cwgstreet/cloudSmoker/Enclosure/models/EC11 rotary encoder/ec11-rotary-encoder2.png

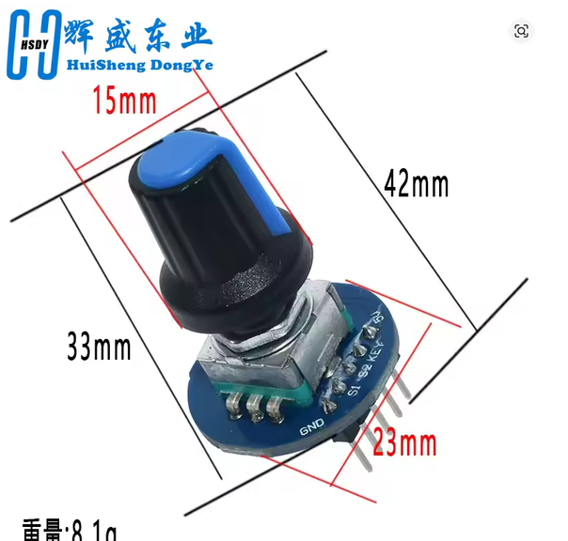
Enclosure/models/EC11 rotary encoder/ec11-rotary-encoder2.png
