cwgstreet/cloudSmoker/Enclosure/models/EC11 rotary encoder/ec11-rotary-encoder.png

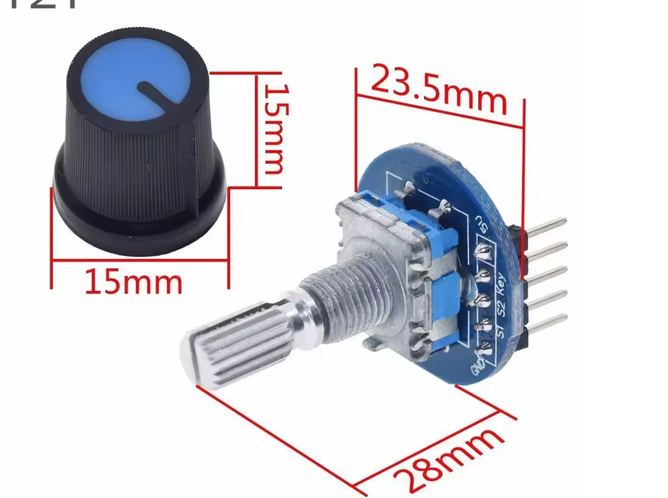
Enclosure/models/EC11 rotary encoder/ec11-rotary-encoder.png
