cwgstreet/cloudSmoker/Enclosure/models/GC9A01_display/GC9A01_display-dimensions.jpg

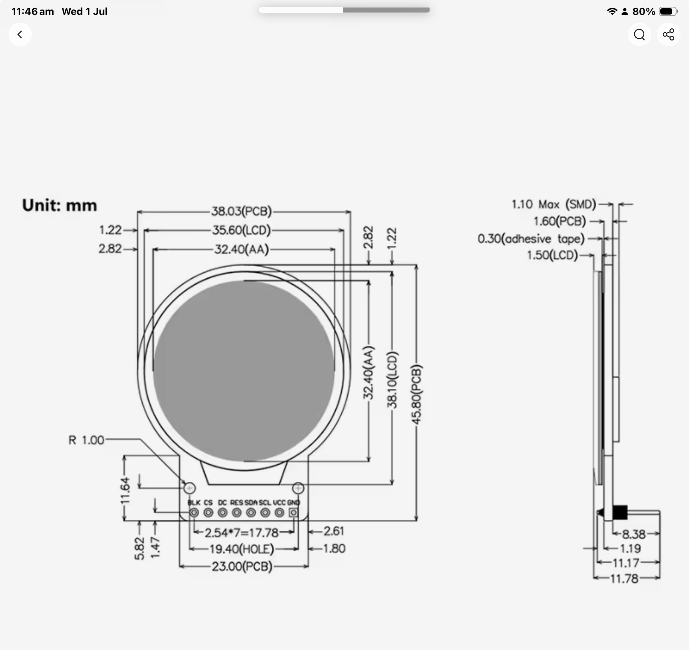
Enclosure/models/GC9A01_display/GC9A01_display-dimensions.jpg
