cwgstreet/cloudSmoker/Hardware/KiCad9/svg_files/ADS-thermistor_closeup.png

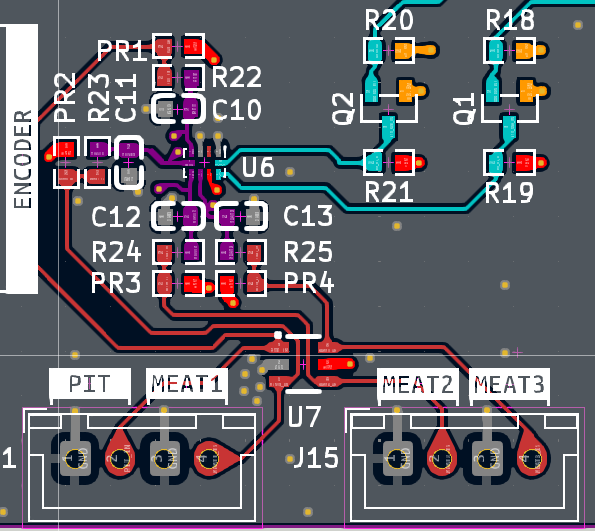
Hardware/KiCad9/svg_files/ADS-thermistor_closeup.png
