cwgstreet/cloudSmoker/Hardware/KiCad9/svg_files/pcb_dashboard2.png

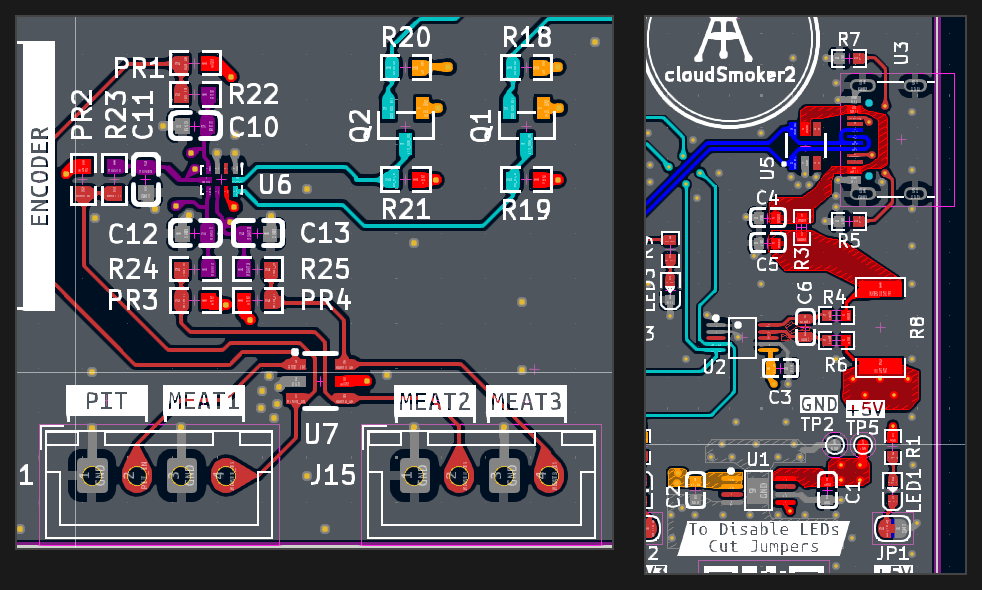
Hardware/KiCad9/svg_files/pcb_dashboard2.png
