cwgstreet/cloudSmoker/Hardware/KiCad9/svg_files/view1_all.png

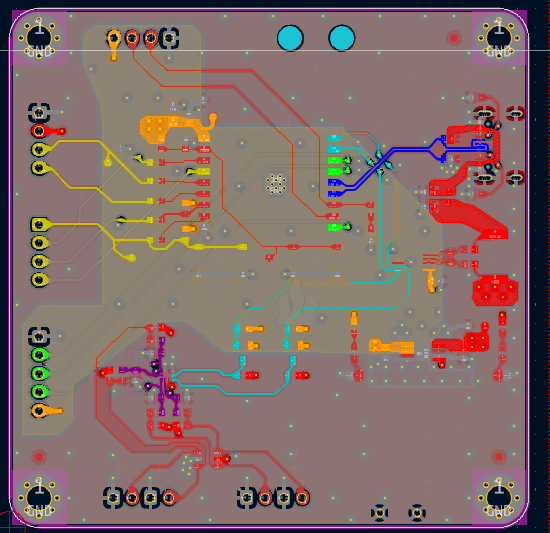
Hardware/KiCad9/svg_files/view1_all.png
