cwgstreet/cloudSmoker/Hardware/KiCad9/svg_files/view2_top.png

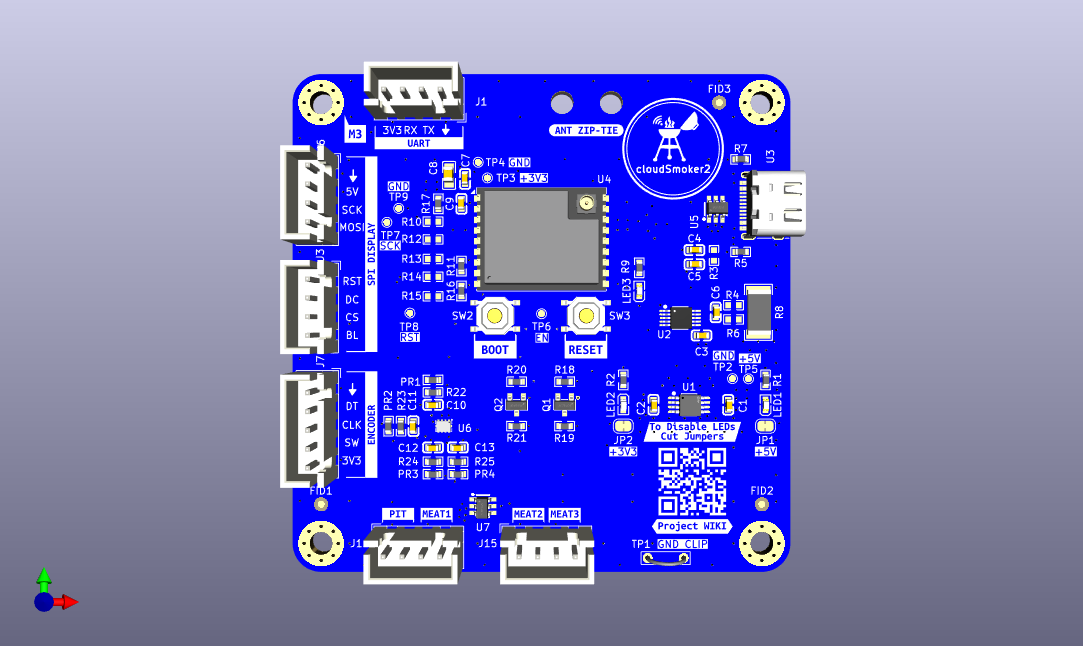
Hardware/KiCad9/svg_files/view2_top.png
