cwgstreet/cloudSmoker/Images/2-CH Logic Level Converter.jpg

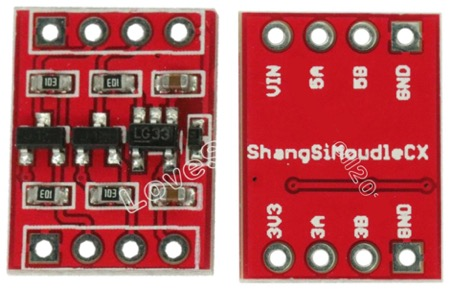
Images/2-CH Logic Level Converter.jpg
