cwgstreet/cloudSmoker/Images/Breadboard2.jpg

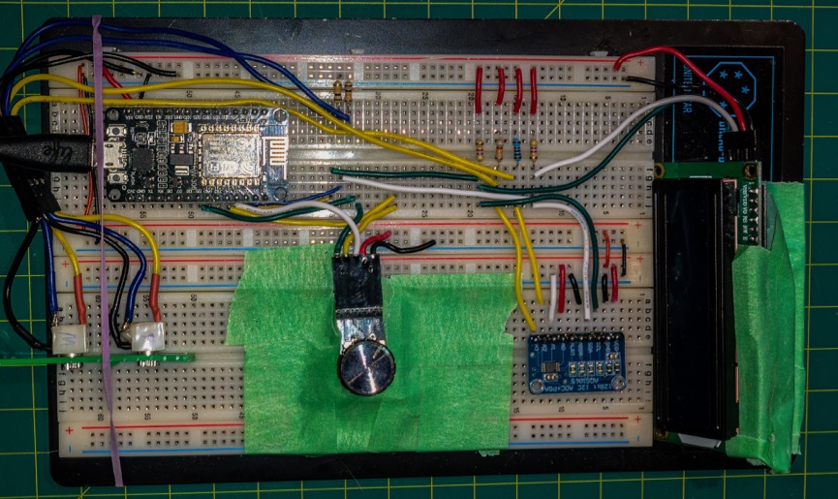
Images/Breadboard2.jpg
