cwgstreet/cloudSmoker/Images/Breadboard.jpg

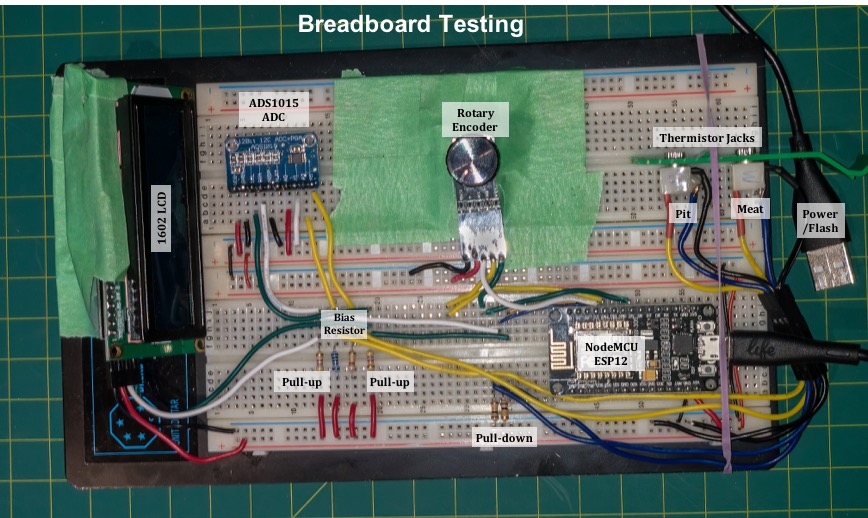
Images/Breadboard.jpg
