cwgstreet/cloudSmoker/Images/CD4066 equivalent pin out.jpg

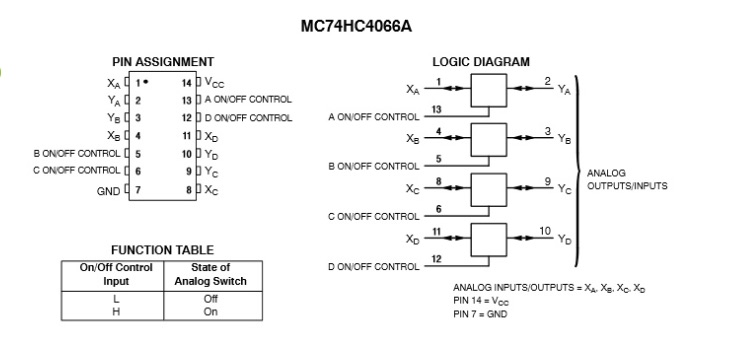
Images/CD4066 equivalent pin out.jpg
