cwgstreet/cloudSmoker/Images/CloudSmoker2 graphic.png

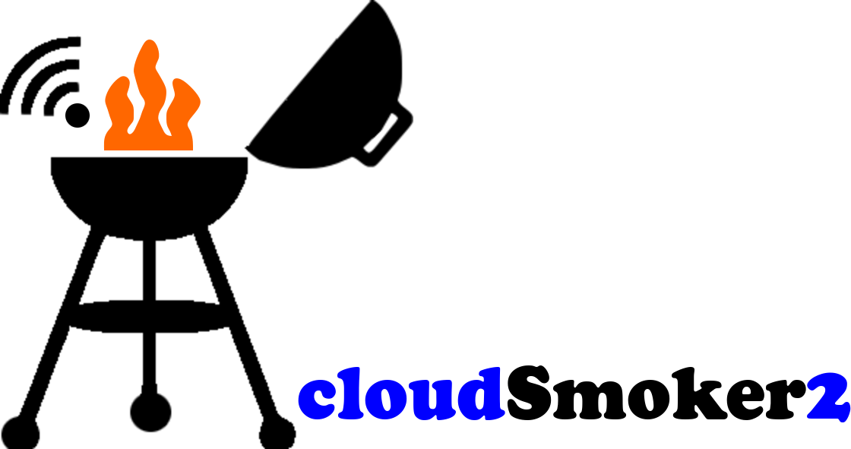
Images/CloudSmoker2 graphic.png
