cwgstreet/cloudSmoker/Images/cloudSmoker2_breadboard_powered.jpg

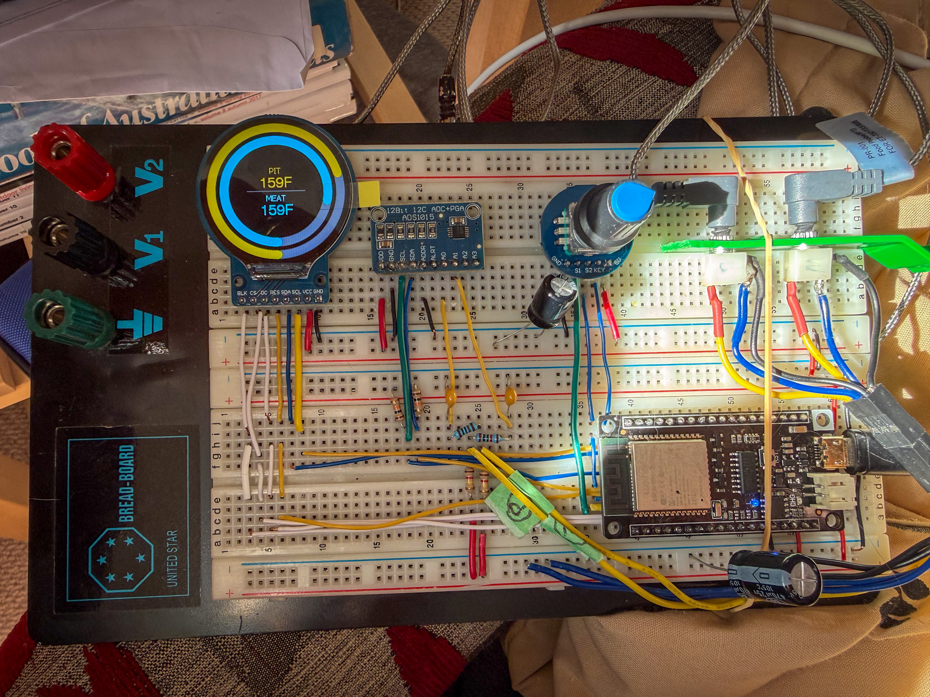
Images/cloudSmoker2_breadboard_powered.jpg
