cwgstreet/cloudSmoker/Images/cloudSmoker2_breadboard_with_ESP32 annotated.jpg

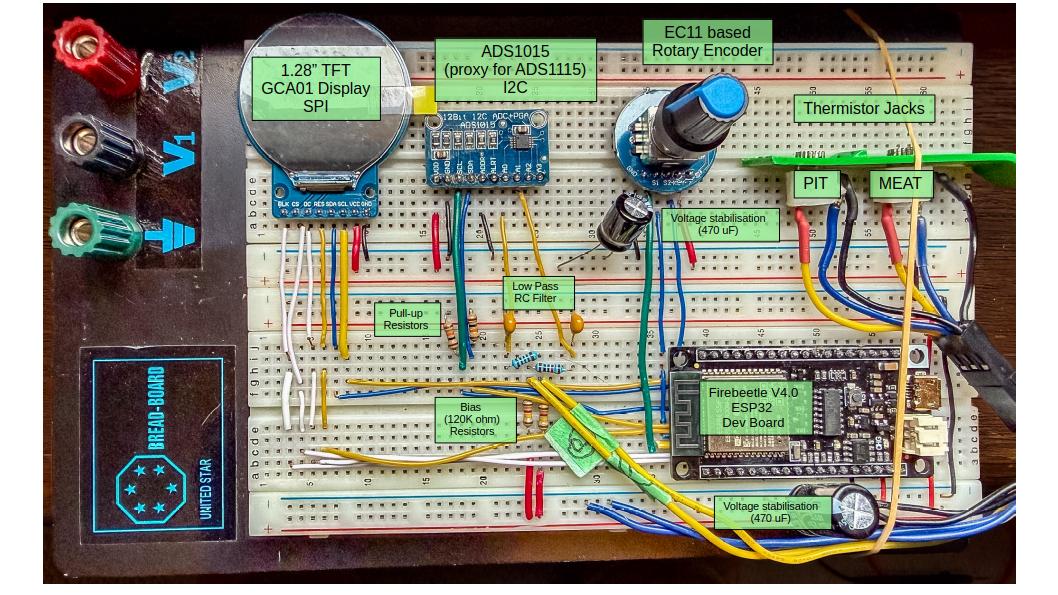
Images/cloudSmoker2_breadboard_with_ESP32 annotated.jpg
