cwgstreet/cloudSmoker/Images/cloudSmoker2_breadboard_with_ESP32.jpg

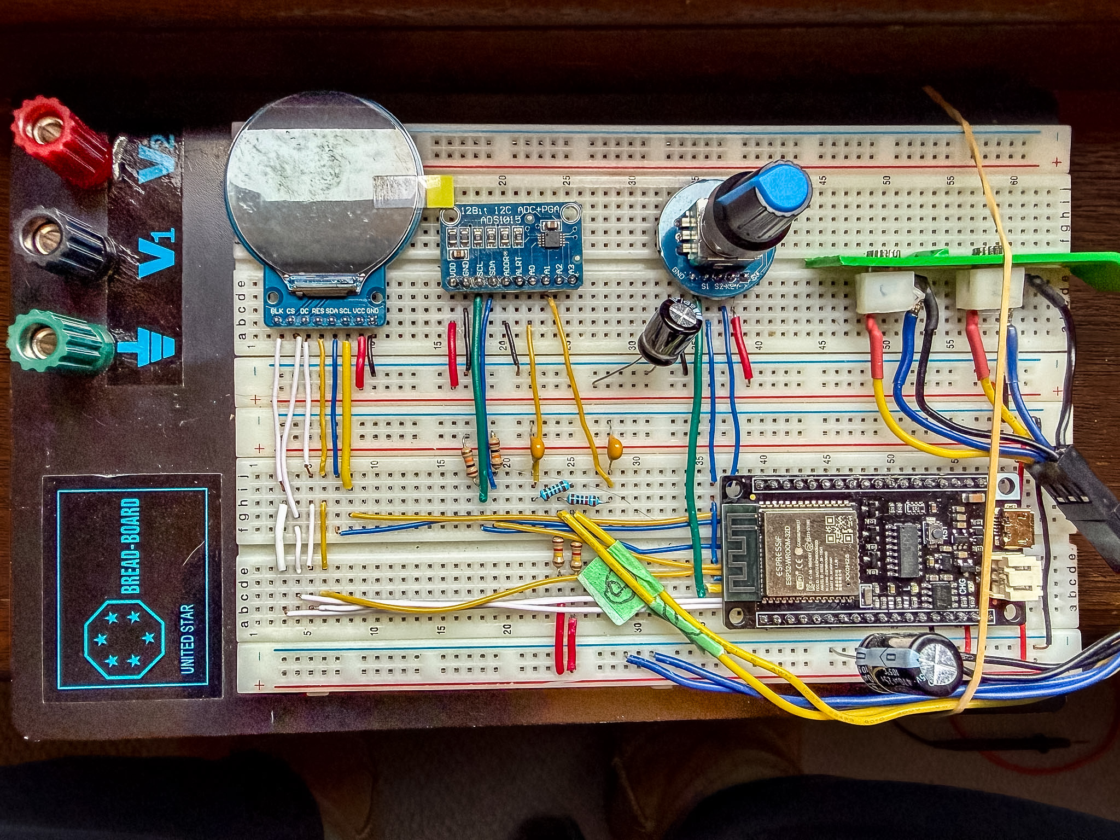
Images/cloudSmoker2_breadboard_with_ESP32.jpg
