cwgstreet/cloudSmoker/Images/cloudSmoker2_breadboard_without_ESP32.jpg

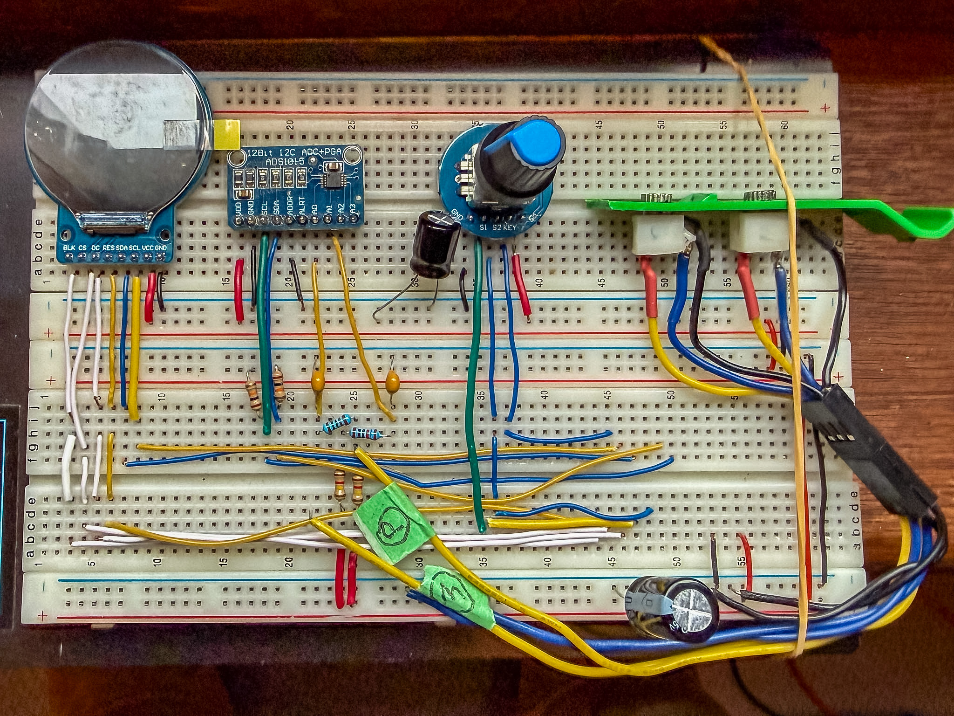
Images/cloudSmoker2_breadboard_without_ESP32.jpg
