cwgstreet/cloudSmoker/Images/cloudSmoker2_display_powered.jpg

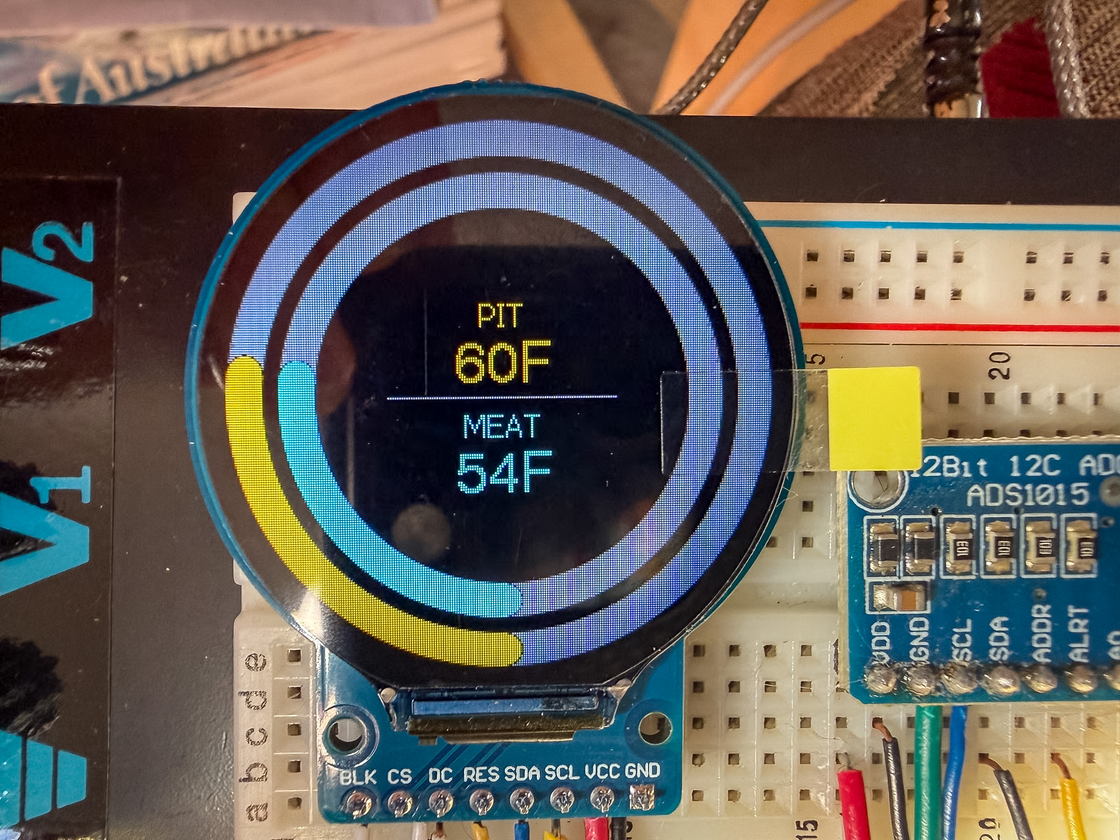
Images/cloudSmoker2_display_powered.jpg
