cwgstreet/cloudSmoker/Images/cloudSmoker brisket dashboard.png

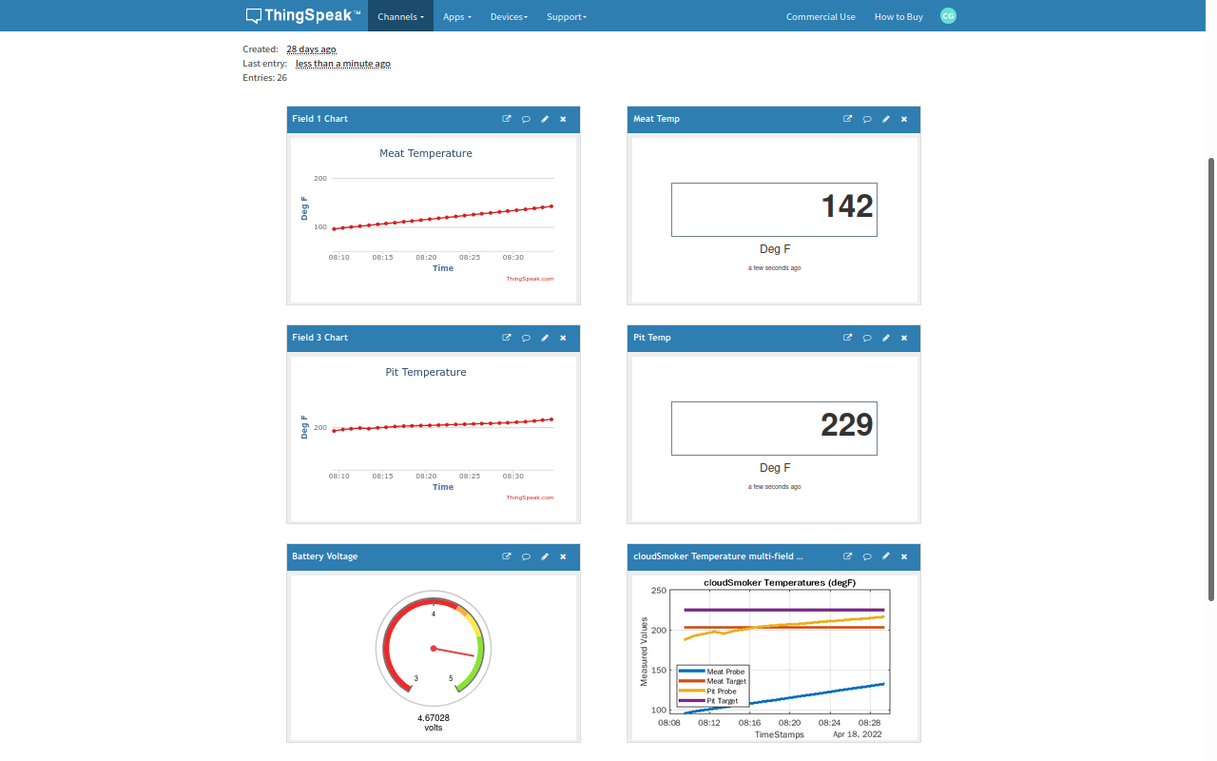
Images/cloudSmoker brisket dashboard.png
