cwgstreet/cloudSmoker/Images/CloudSmoker state diagram2.jpg

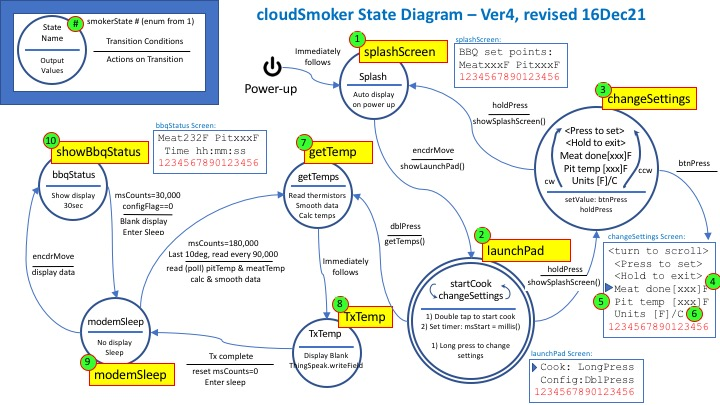
Images/CloudSmoker state diagram2.jpg
