cwgstreet/cloudSmoker/Images/CloudSmoker-breadboard.jpg

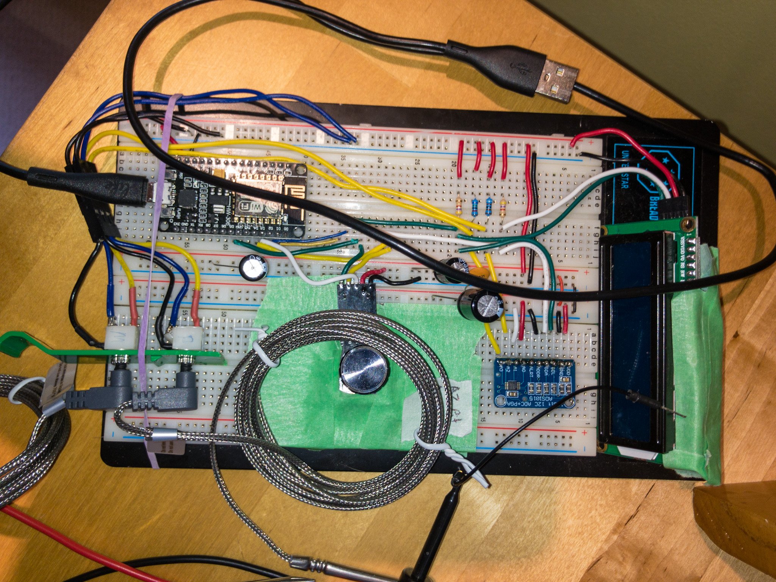
Images/CloudSmoker-breadboard.jpg
