cwgstreet/cloudSmoker/Images/cloudSmoker-fritzing.jpg

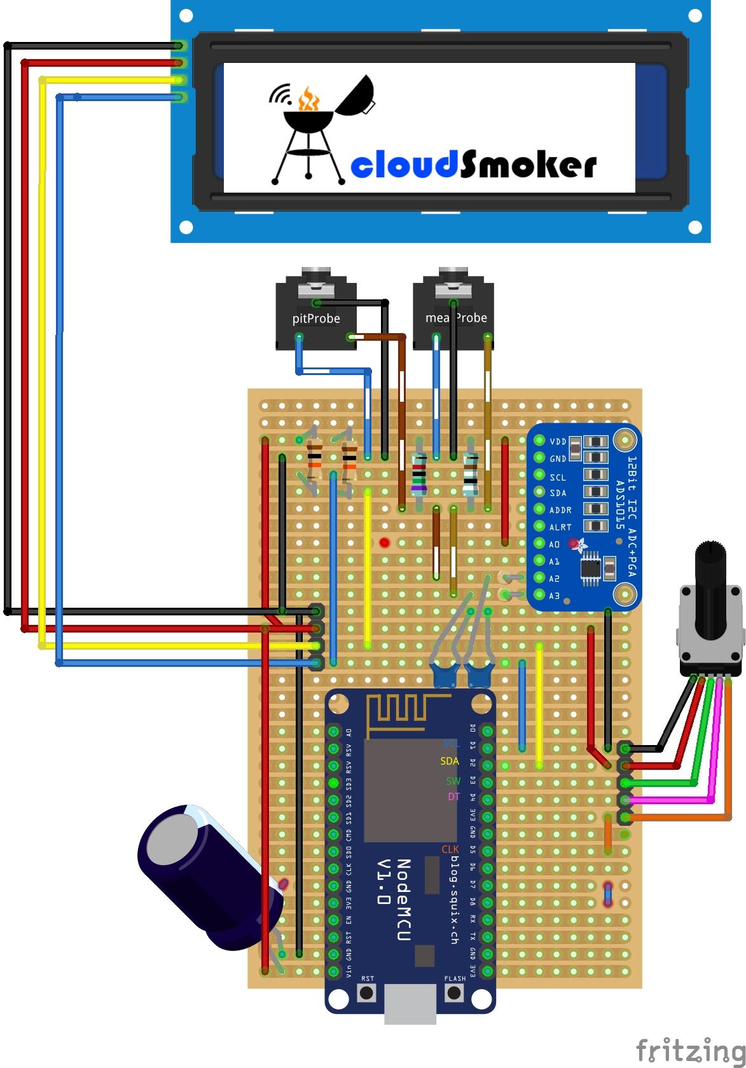
Images/cloudSmoker-fritzing.jpg
