cwgstreet/cloudSmoker/Images/CloudSmoker_breadboard_labelled.jpg

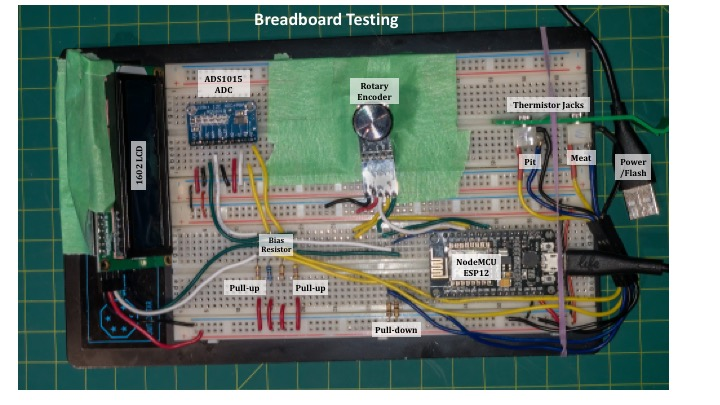
Images/CloudSmoker_breadboard_labelled.jpg
