cwgstreet/cloudSmoker/Images/cloudSmoker_ver2f-bottom-down.png

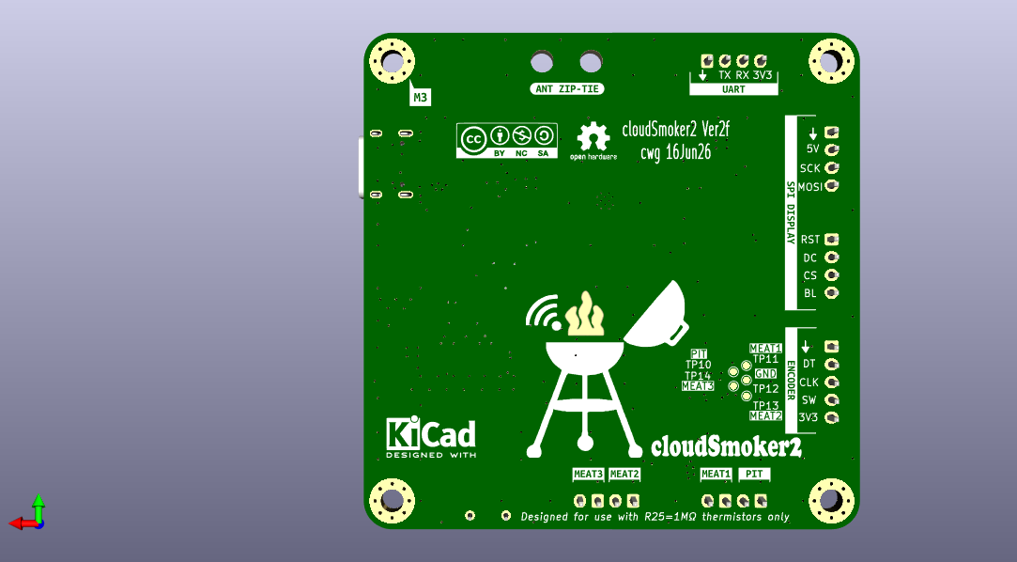
Images/cloudSmoker_ver2f-bottom-down.png
