cwgstreet/cloudSmoker/Images/cloudSmoker_ver2f-top-down.png

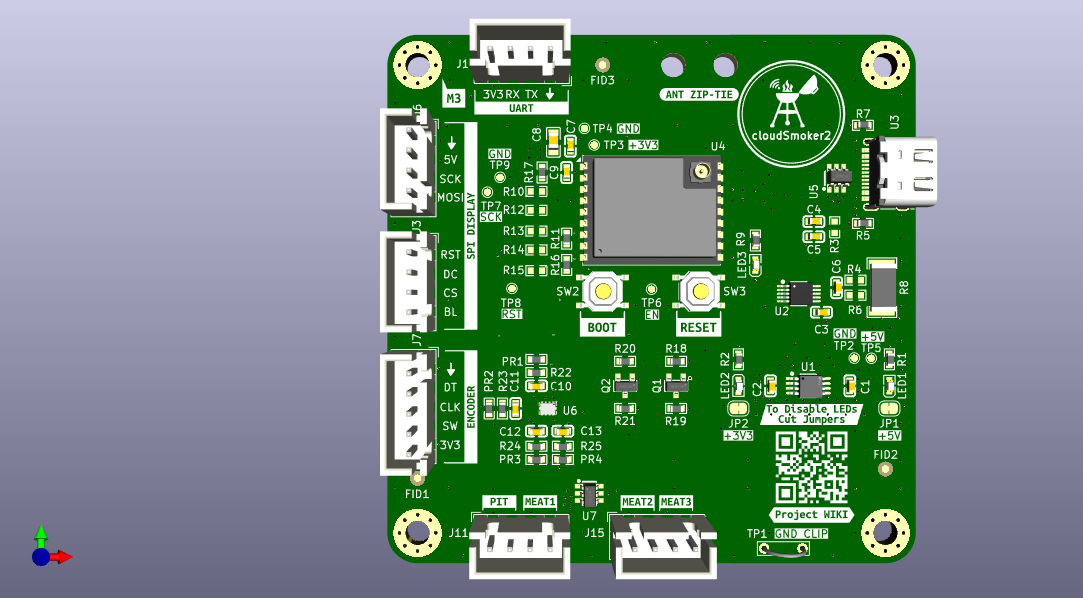
Images/cloudSmoker_ver2f-top-down.png
