cwgstreet/cloudSmoker/Images/Cook Images/bbq-going.JPG

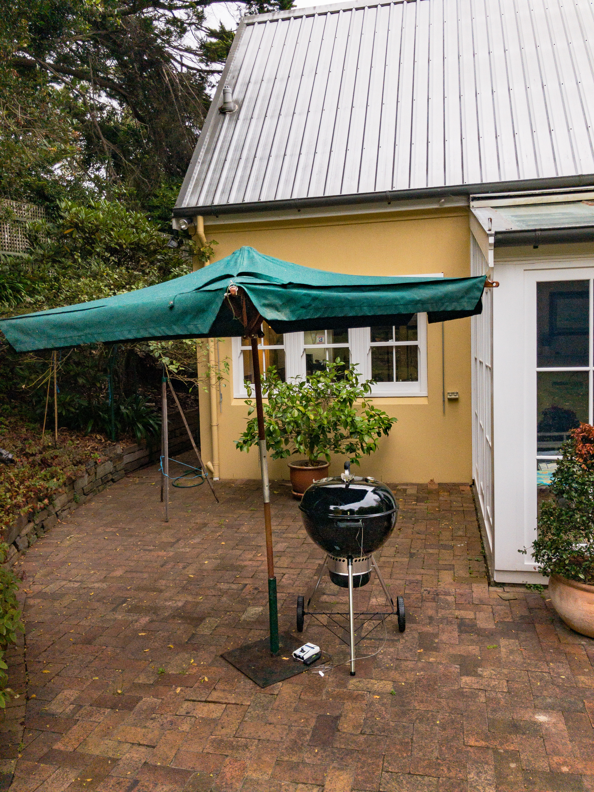
Images/Cook Images/bbq-going.JPG
