cwgstreet/cloudSmoker/Images/Cook Images/brisket-final-with-log.JPG

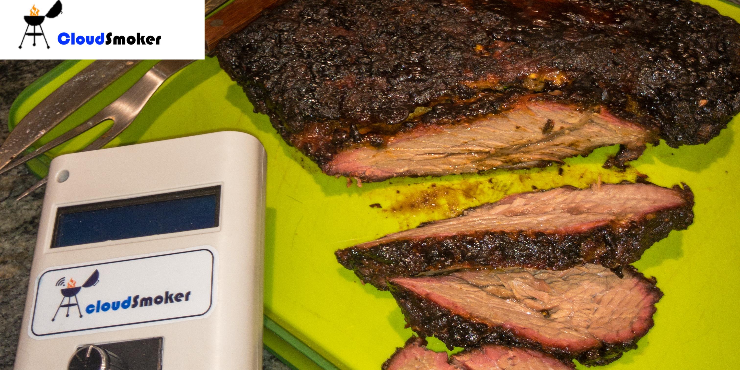
Images/Cook Images/brisket-final-with-log.JPG
