cwgstreet/cloudSmoker/Images/Cook Images/brisket-off.JPG

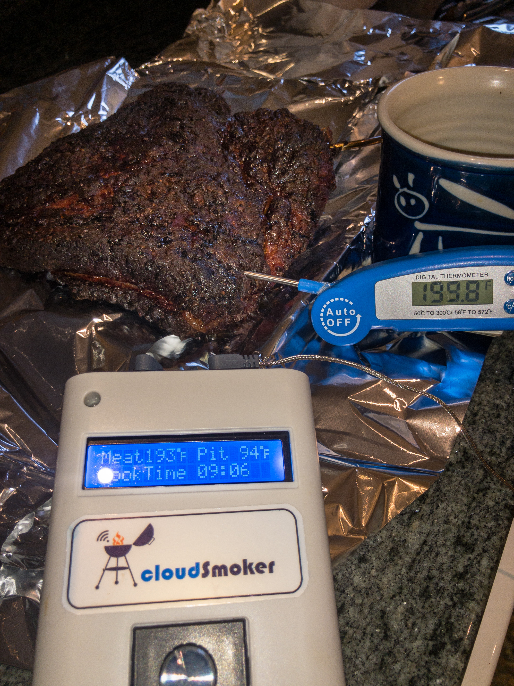
Images/Cook Images/brisket-off.JPG
