cwgstreet/cloudSmoker/Images/Cook Images/cloisSmoker-working.JPG

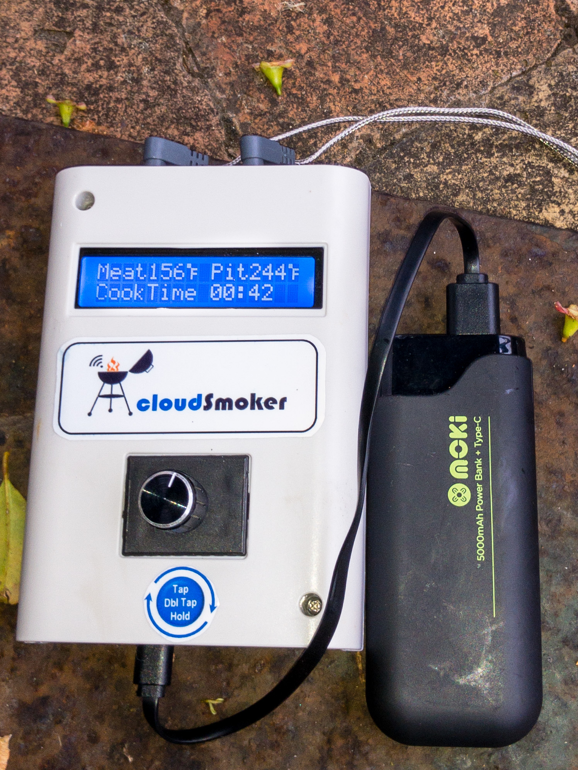
Images/Cook Images/cloisSmoker-working.JPG
