cwgstreet/cloudSmoker/Images/Cook Images/cloudSmoker-project-boxed.JPG

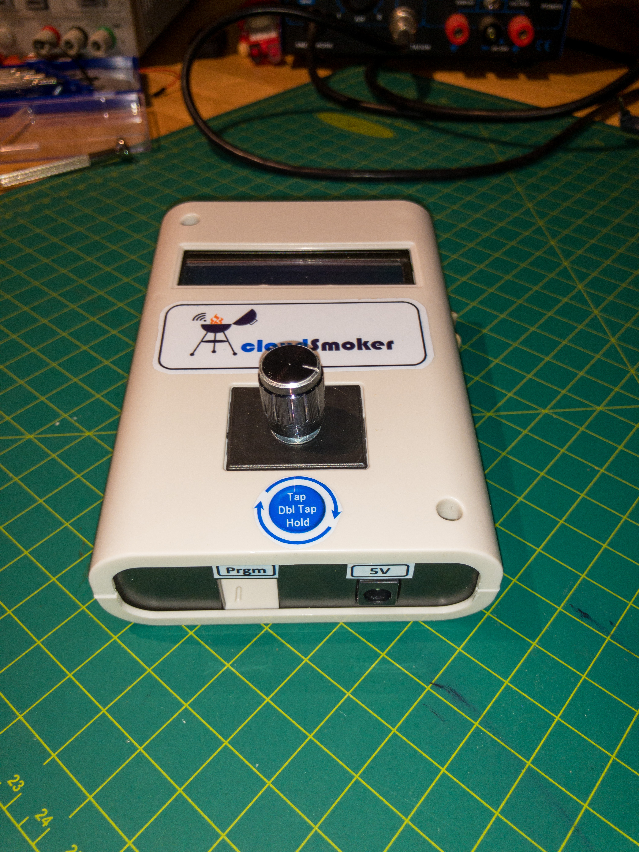
Images/Cook Images/cloudSmoker-project-boxed.JPG
