cwgstreet/cloudSmoker/Images/Cook Images/uncooked-brisket.JPG

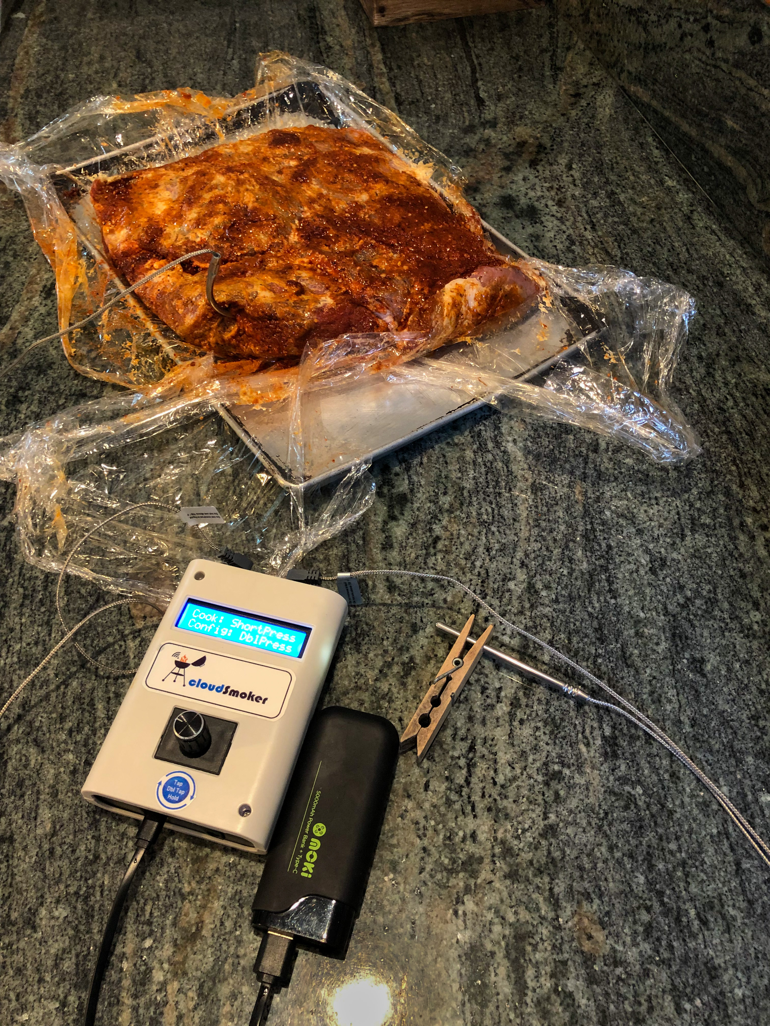
Images/Cook Images/uncooked-brisket.JPG
