cwgstreet/cloudSmoker/Images/external_antenna.png

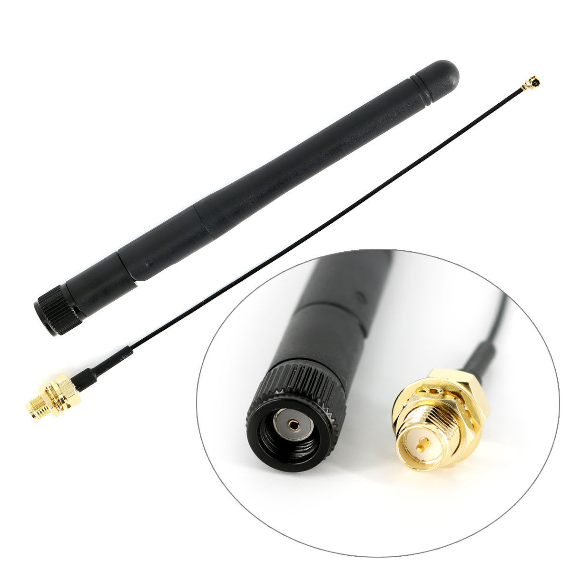
Images/external_antenna.png
