cwgstreet/cloudSmoker/Images/grounded 732 probe.jpg

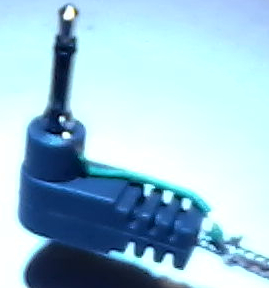
Images/grounded 732 probe.jpg
