cwgstreet/cloudSmoker/Images/lcd_1602.jpg

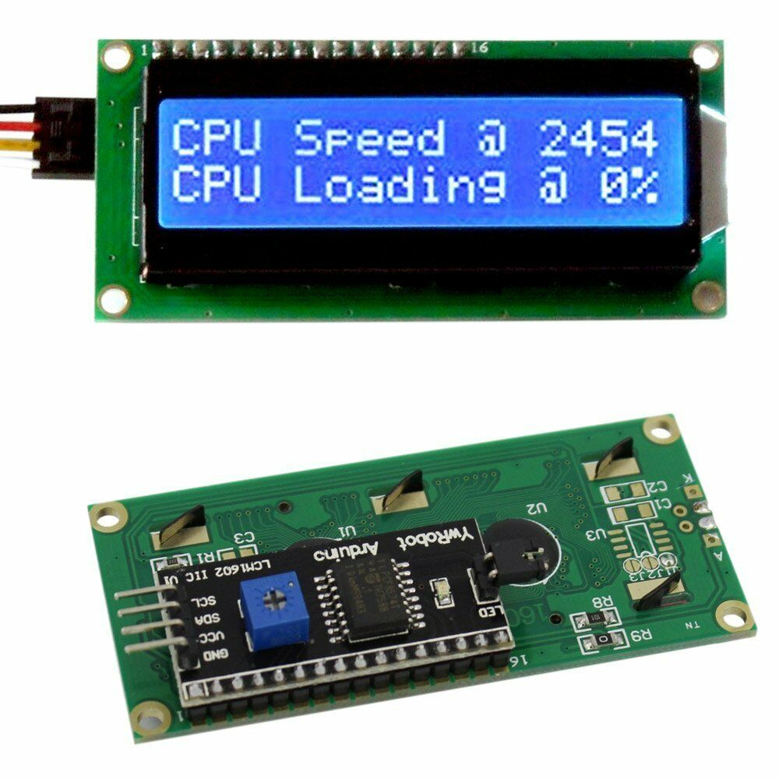
Images/lcd_1602.jpg
