cwgstreet/cloudSmoker/Images/lm358_opamp_smd.jpg

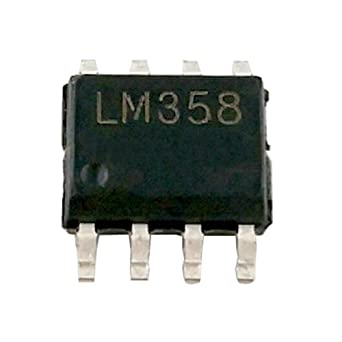
Images/lm358_opamp_smd.jpg
