cwgstreet/cloudSmoker/Images/Maverick probe.jpg

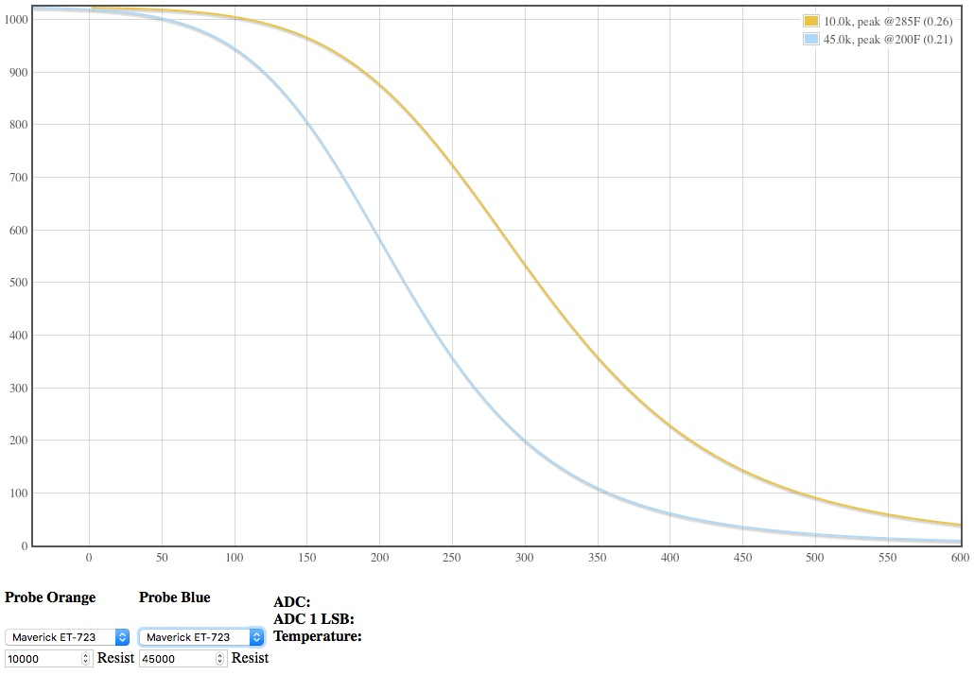
Images/Maverick probe.jpg
