cwgstreet/cloudSmoker/Images/Maverick probes volt div output.png

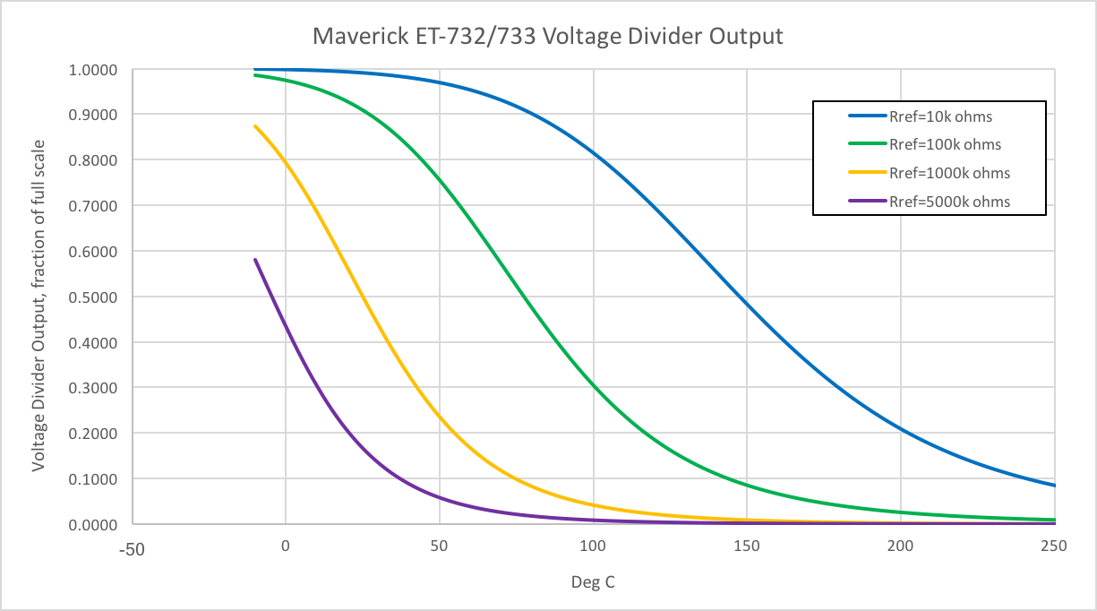
Images/Maverick probes volt div output.png
