cwgstreet/cloudSmoker/Images/Maverick probes volt div sensitivity optimised.png

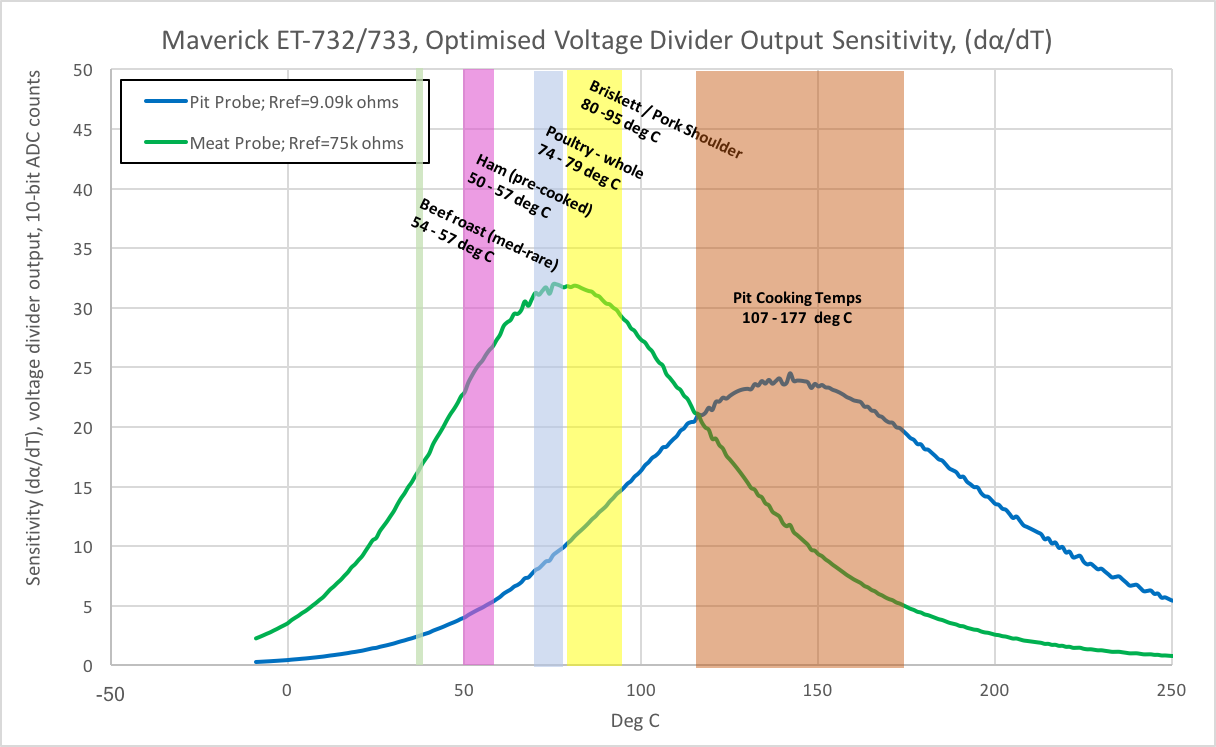
Images/Maverick probes volt div sensitivity optimised.png
