cwgstreet/cloudSmoker/Images/Maverick probes volt div sensitivity unoptimised.png

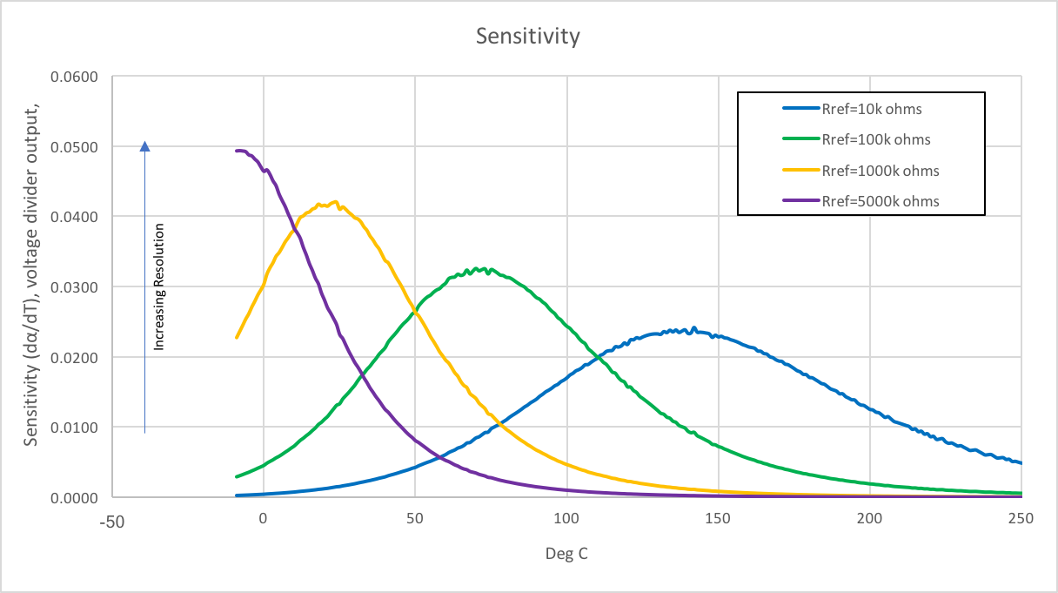
Images/Maverick probes volt div sensitivity unoptimised.png
