cwgstreet/cloudSmoker/Images/MeatProbe error.jpg

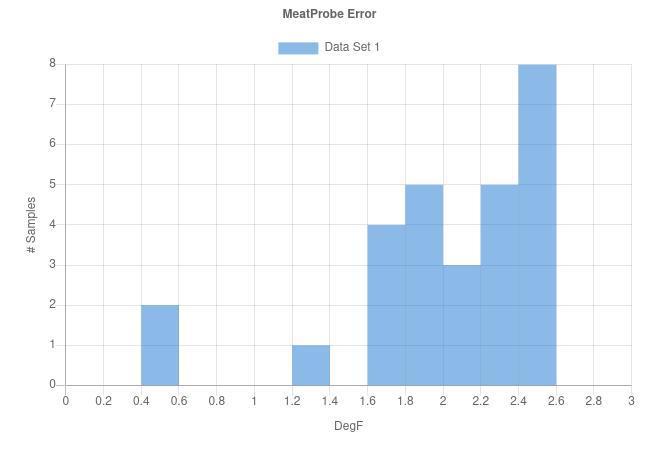
Images/MeatProbe error.jpg
