cwgstreet/cloudSmoker/Images/non-inverting opamp level shifter.jpg

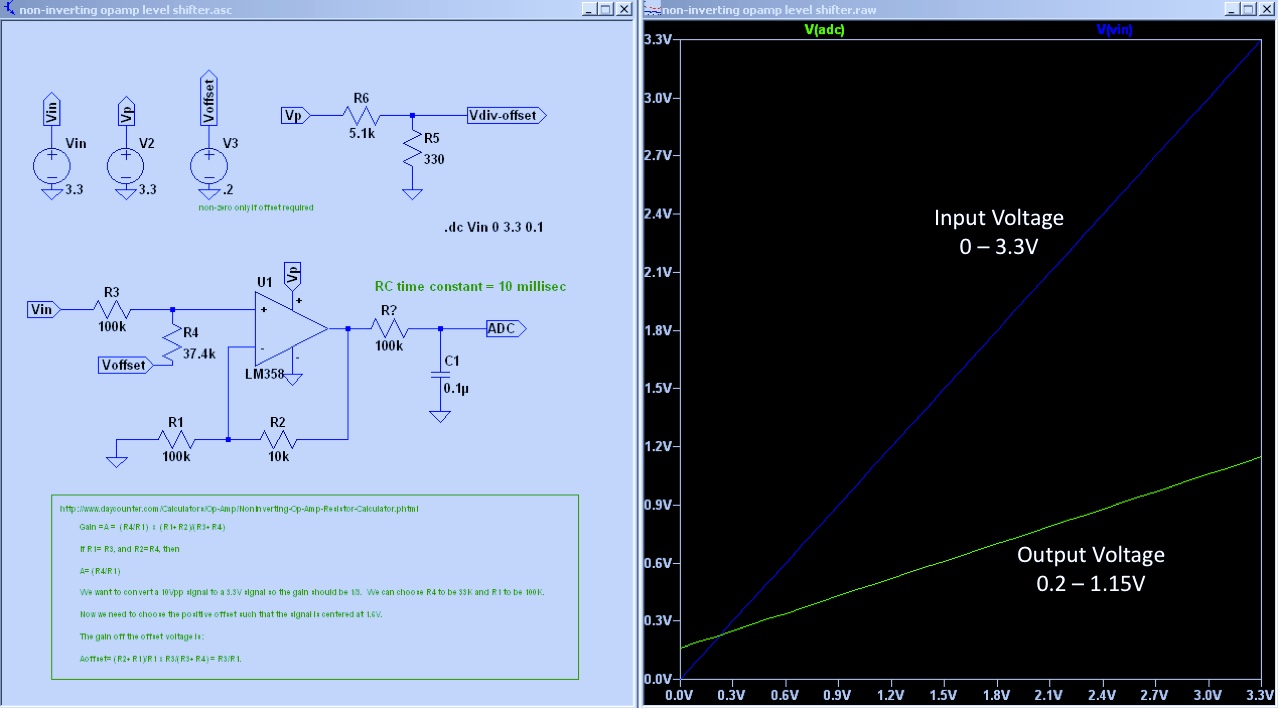
Images/non-inverting opamp level shifter.jpg
