cwgstreet/cloudSmoker/Images/PitProbe Temp Error.jpg

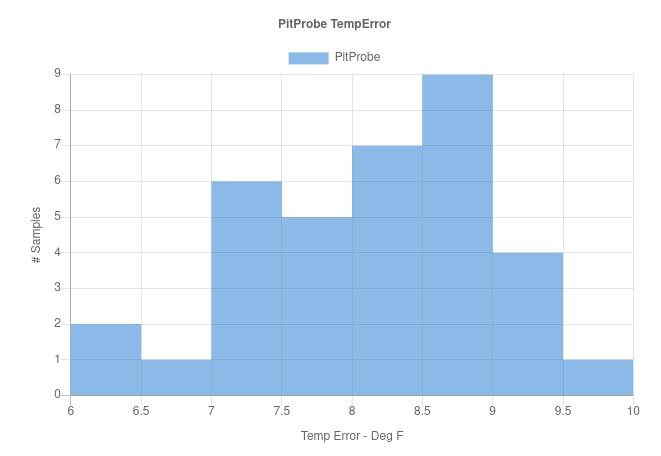
Images/PitProbe Temp Error.jpg
