cwgstreet/cloudSmoker/Images/Power filtered thermister circuit.JPG

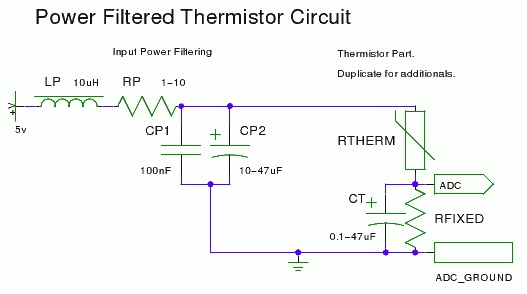
Images/Power filtered thermister circuit.JPG
