cwgstreet/cloudSmoker/Images/RC-filter-ADC-cloudSmoker.jpg

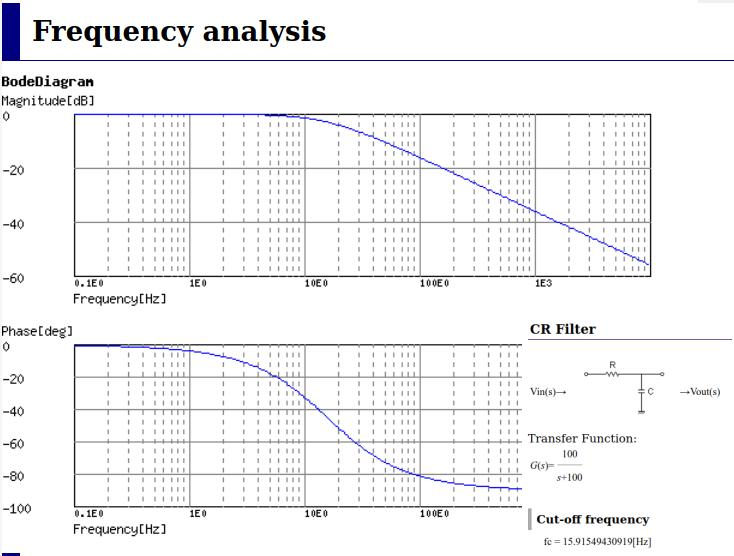
Images/RC-filter-ADC-cloudSmoker.jpg
