cwgstreet/cloudSmoker/Images/RC-filter.jpg

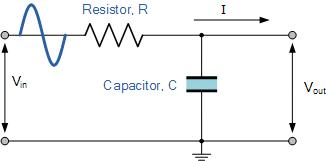
Images/RC-filter.jpg
