cwgstreet/cloudSmoker/Images/Semitek GT-2 thermistor res vs temp.jpg

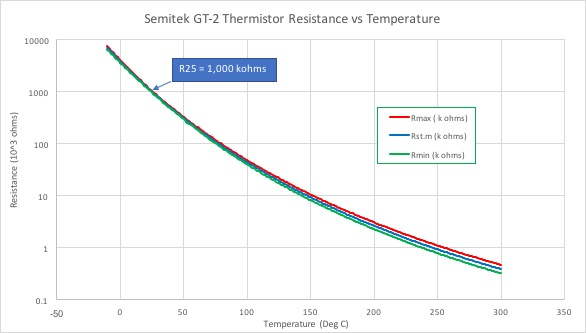
Images/Semitek GT-2 thermistor res vs temp.jpg
