cwgstreet/cloudSmoker/Images/Steinhart-Hart Coefficients calculation.png

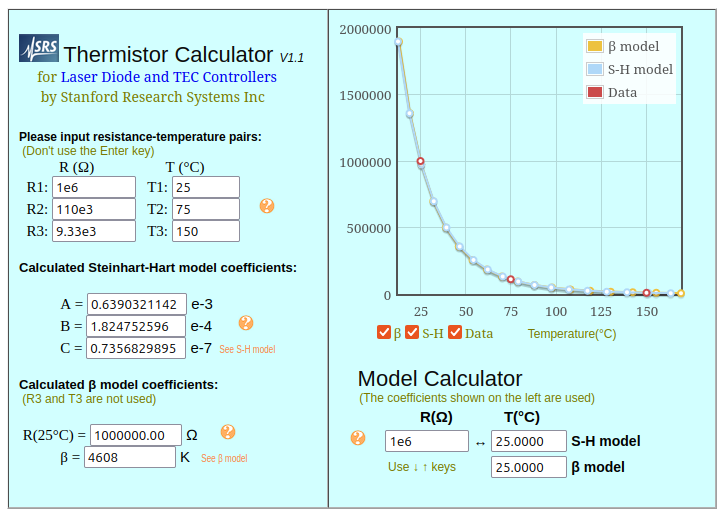
Images/Steinhart-Hart Coefficients calculation.png
