cwgstreet/cloudSmoker/Images/temp probes with pullups and RC filter.png

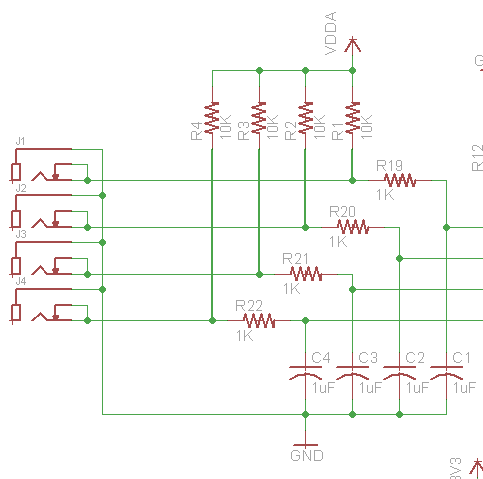
Images/temp probes with pullups and RC filter.png
