cwgstreet/cloudSmoker/Images/Thermistor voltage divider.jpg

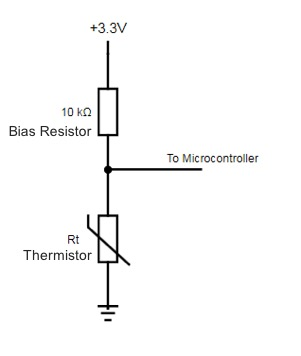
Images/Thermistor voltage divider.jpg
