cwgstreet/cloudSmoker/Images/Version-voltage-temp-comparison.png

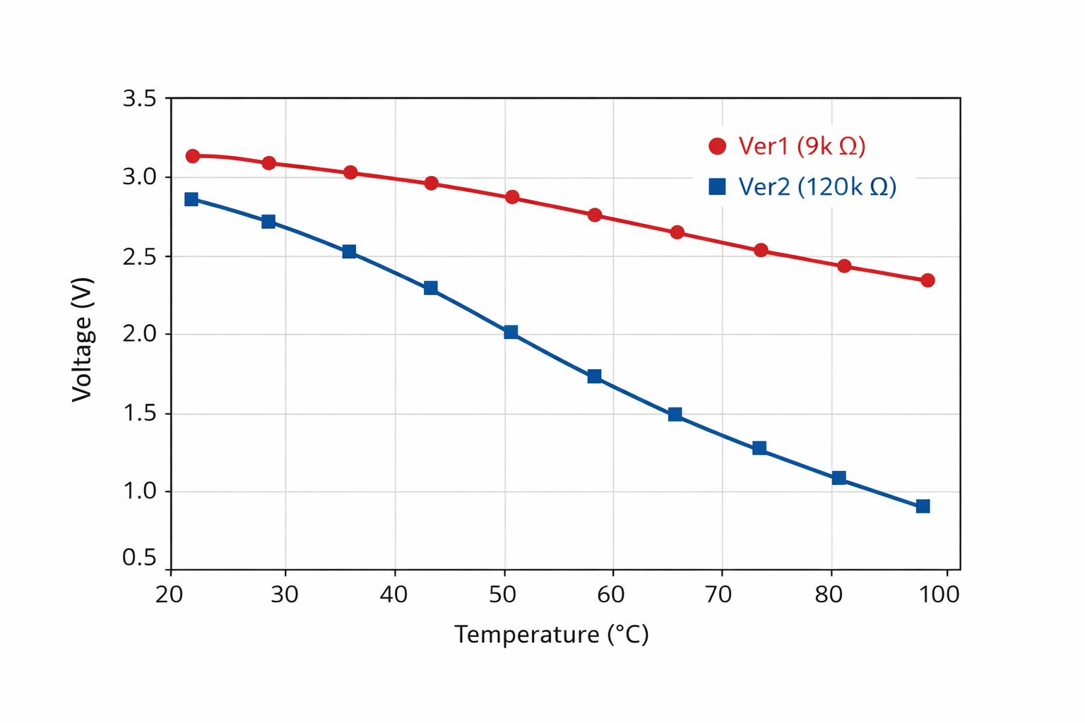
Images/Version-voltage-temp-comparison.png
