cwgstreet/cloudSmoker/Enclosure/print_files/cloudSmoker2_ver2b_top_enclosure.step

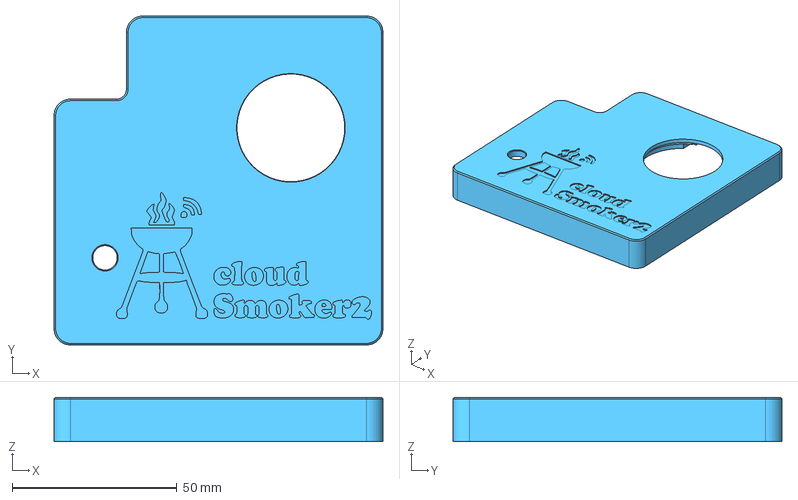
[picture p79: CAD file, 2026-10-05]
Enclosure/print_files/cloudSmoker2_ver2b_top_enclosure.step
100.0 x 100.0 x 13.5 mm
