cwgstreet/cloudSmoker/Images/cloudSmoker2_top_enclosure_multi-colour_print.jpg

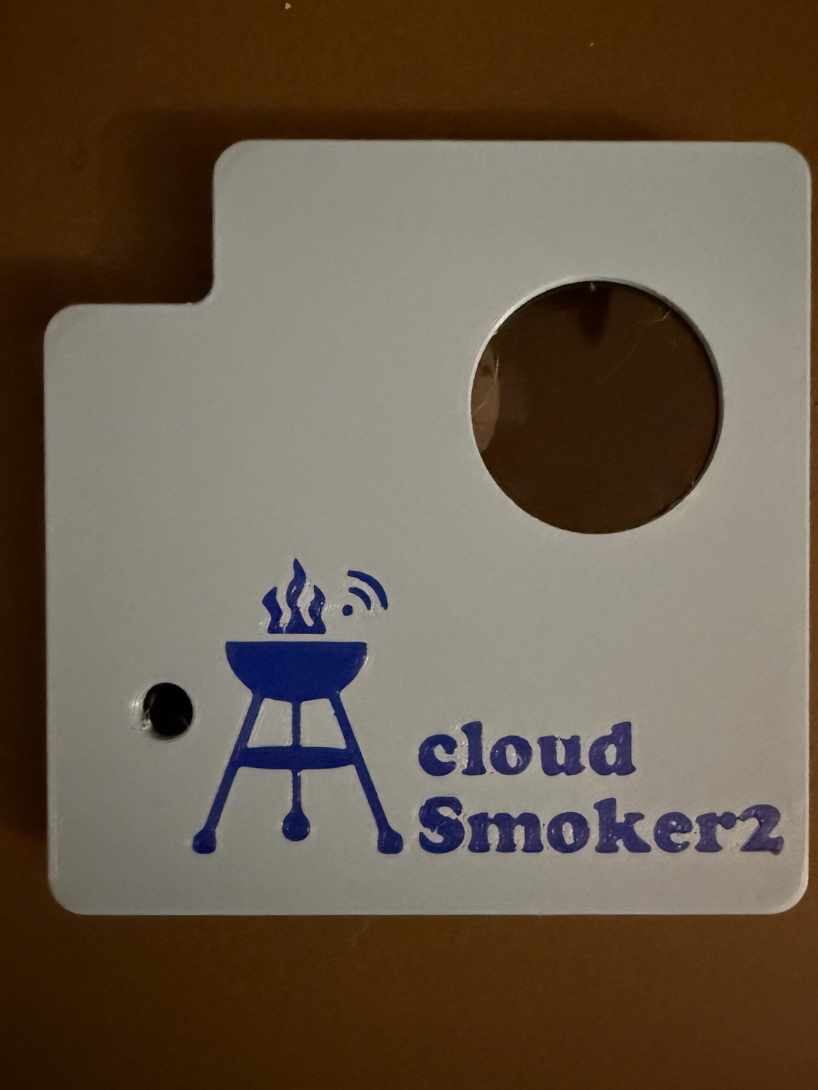
Images/cloudSmoker2_top_enclosure_multi-colour_print.jpg
