cwgstreet/cloudSmoker/Images/Construction Images/built.jpg

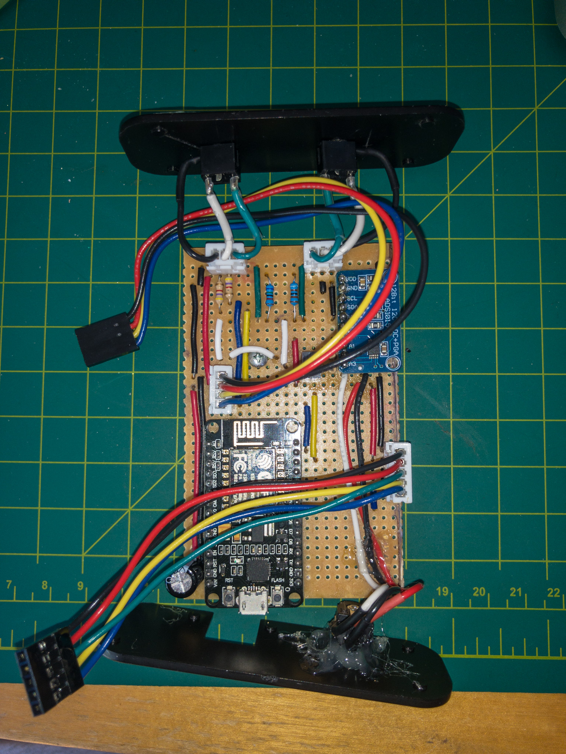
Images/Construction Images/built.jpg
