cwgstreet/cloudSmoker/Images/Construction Images/construction.jpg

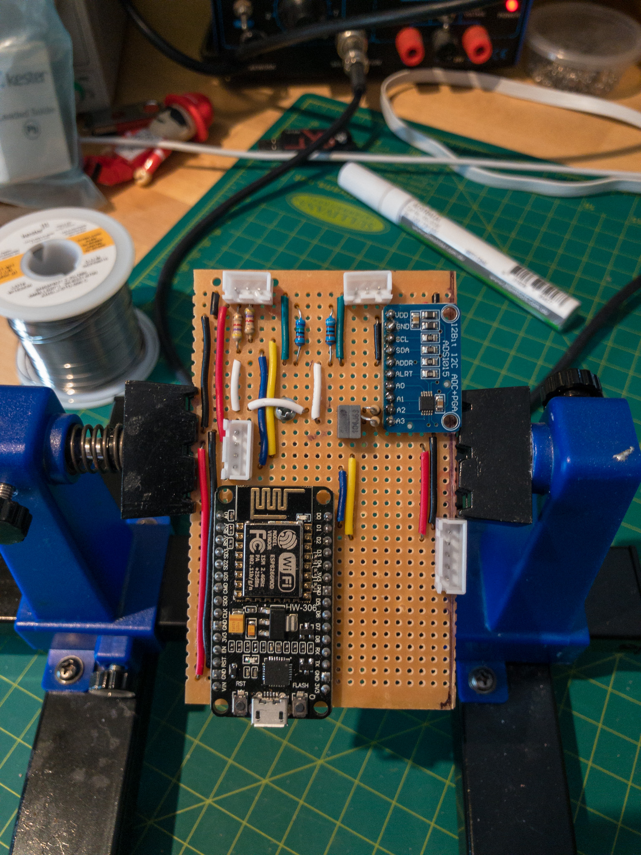
Images/Construction Images/construction.jpg
