cwgstreet/cloudSmoker/Images/Construction Images/cutting-traces.jpg

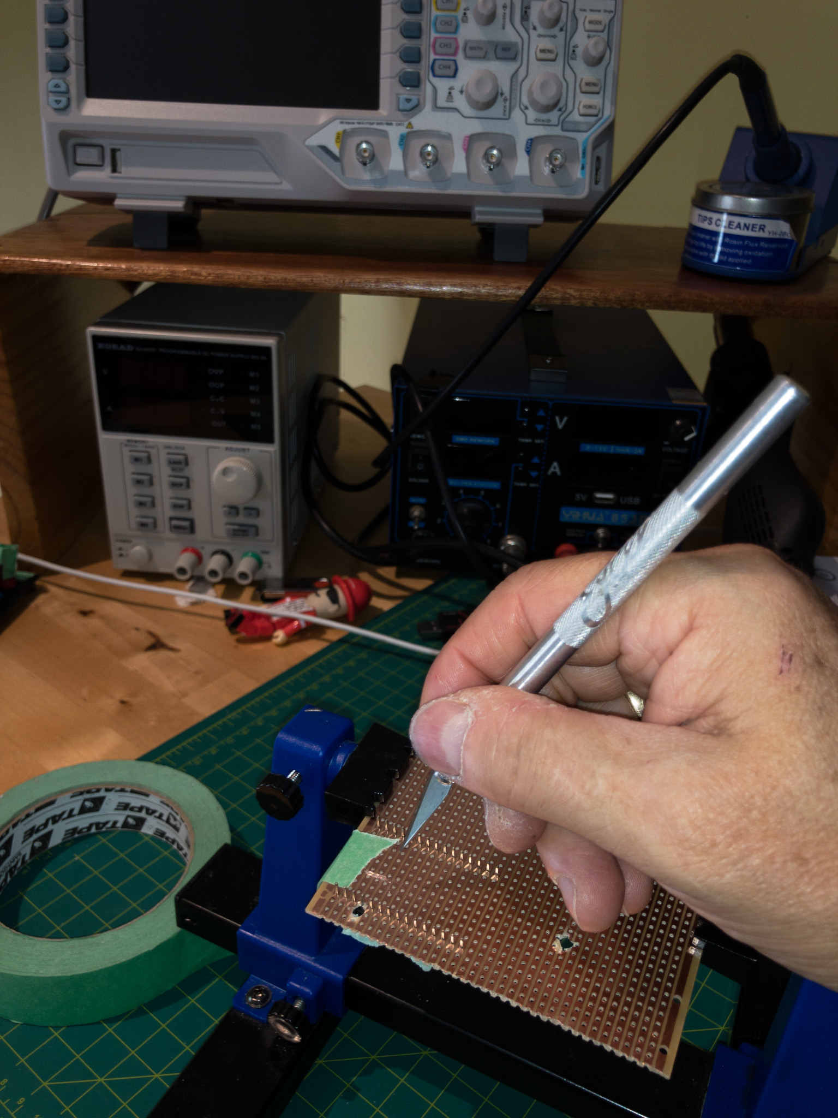
Images/Construction Images/cutting-traces.jpg
