cwgstreet/cloudSmoker/Images/Construction Images/final-box-labelled.jpg

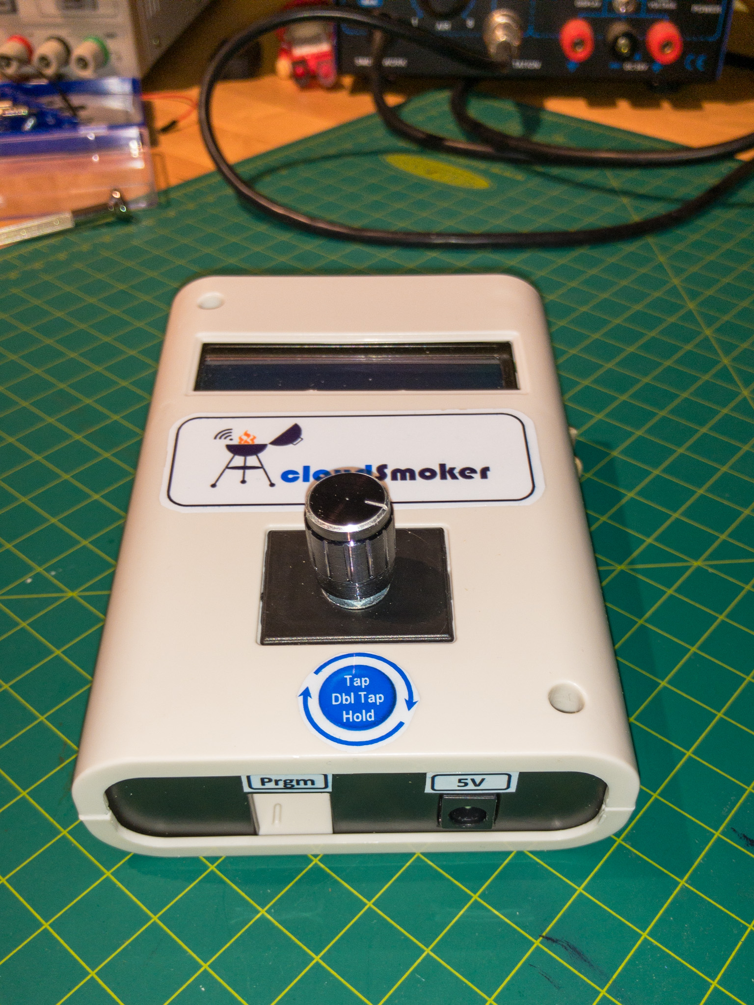
Images/Construction Images/final-box-labelled.jpg
