cwgstreet/cloudSmoker/Images/Construction Images/final-box-with-probes.jpg

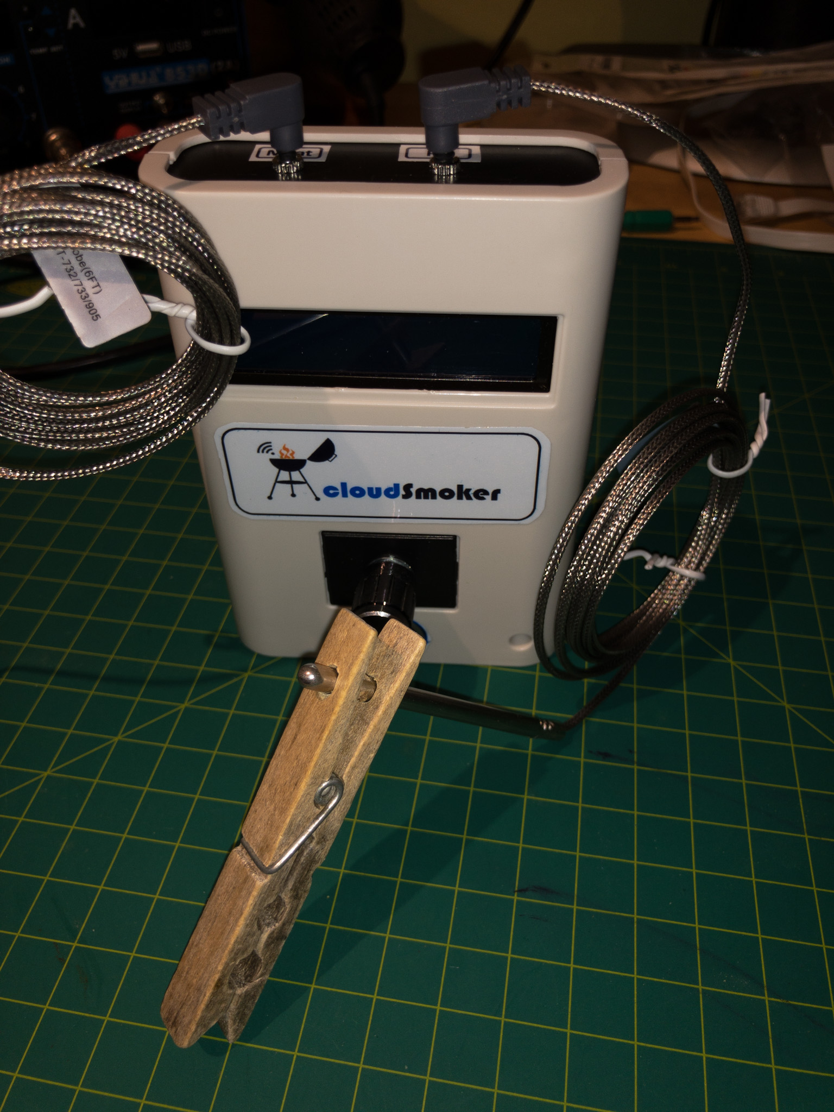
Images/Construction Images/final-box-with-probes.jpg
