cwgstreet/cloudSmoker/Images/Construction Images/nearly-built.jpg

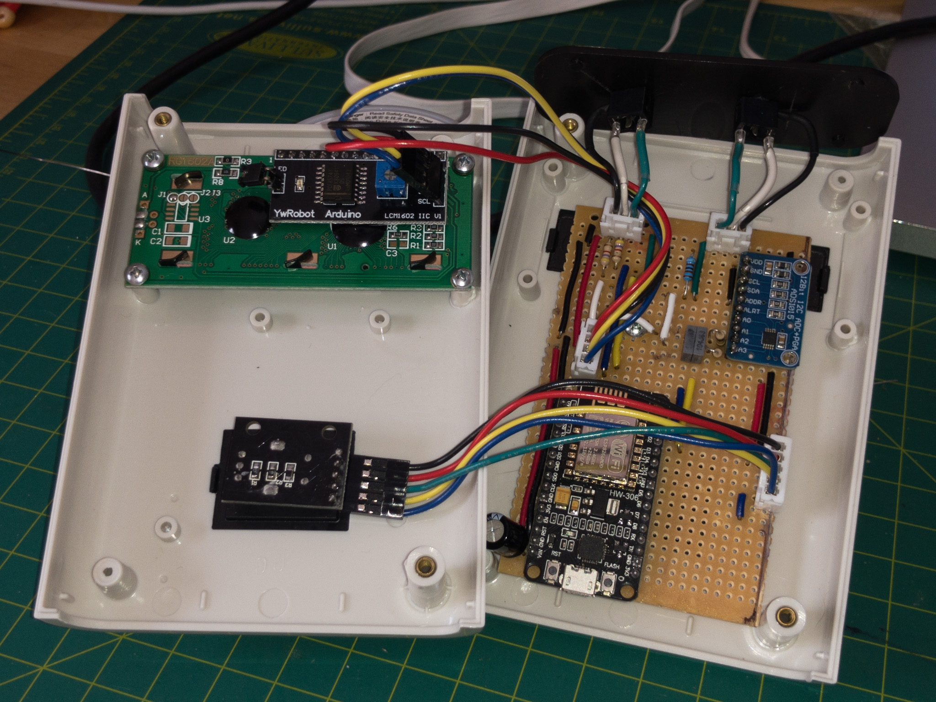
Images/Construction Images/nearly-built.jpg
