cwgstreet/cloudSmoker/include/secretsTemplate.h

/* ***************************************************************
 * secretsTemplate.h - template library listing confidential constants
 *   usernames, passwords, API keys and similar
 *   >>>>> NO CONFIDENTIAL DATA IN THIS FILE _ JUST PLACEHOLDER NAMES <<<<<<<
 *  Per .gitignore, the actual secrets.h file will not be uploaded into public repository
 *
 *  C W Greenstreet, Ver1, 20Mar2022
 *    MIT Licence - Released into the public domain
 *
 ** ************************************************************* */

//! >>>>> template commented out to prevent multiple variable definition <<<<<


// #ifndef SECRETS_TEMPLATE_H
// #define SECRETS_TEMPLATE_H

// #if ARDUINO >= 100  // this if-else block manages depreciated versions of Arduino IDE
// #include <Arduino.h>
// #else
// #include <WConstants.h>
// #include <WProgram.h>
// #include <pins_arduino.h>
// #endif  // end if-block

// ******************************************************
//?    WiFi Connection Parameters
//!     Not used!  Went with more secure Wifi Manager instead where this info is entered on start-up
// *******************************************************
// const char* SSID = "YOUR_SSID";                    // The SSID (name) of the Wi-Fi network you want to connect to
// const char* WIFI_PASSWORD = "YOUR_WIFI_PASSWORD";  // The password of the Wi-Fi network

// ******************************************************
//?  ThingSpeak Connection Parameters
// *******************************************************/
// const unsigned long THNGSPK_CHANNEL_ID = CHANNEL_ID_NUMBER;   // Replace with Thingspeak Channel ID
// const char* THNGSPK_WRITE_API_KEY = "APIKEY";    // Replace with Thingspeak Write API Key

// includ Read API Key for potential future use:
// const char* THNGSPK_READ_API_KEY = "APIKEY";  // Replace with Thingspeak Read API Key

// #endif  // end header guard
 
